palette-system/az-m5ortho/docs/azm5ortho/wifi_setting/README.md

# Wifi設定画面

<br><br>

## 設定画面の開き方
<table>
  <tr>
    <td></td>
    <td valign="top">
      キーボードを設定モードで再起動します。<br>
      設定モードでの再起動の方法はこちら → <a href="https://github.com/palette-system/az-m5ortho/tree/main/docs/azm5ortho/moniter_setting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" target="_blank">https://github.com/palette-system/az-m5ortho/tree/main/docs/azm5ortho/moniter_setting/</a>
    </td>
  </tr>
  <tr>
    <td></td>
    <td valign="top">
      この状態でPCやスマートフォンからWiFiのアクセスポイントを検索すると「<b>AZ-Keyboard-****</b>」があるので接続します。
    </td>
  </tr>
  <tr>
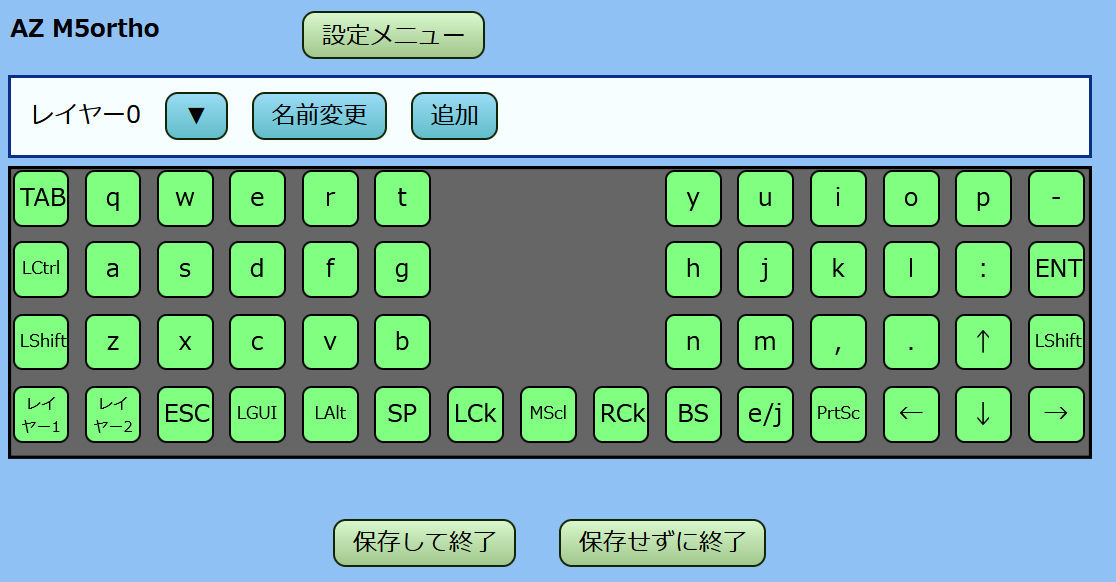
[picture p62: images/azm5ortho/setting_2.jpg]
    <td></td>
    <td valign="top">
      WiFiに接続できるとブラウザが立ち上がり、自動的に設定画面が開きます。
    </td>
  </tr>
</table>

<br><br>

※ 設定画面の操作方法については AZ-Macro の設定マニュアルをご覧下さい。<br>
<a href="https://github.com/palette-system/az-macro/blob/master/docs/az-macro-setting-manual.pdf" target="_blank">AZ-Macro 設定マニュアル</a><br>
<br>
※ アップデートされている箇所がいくつかありますのでこちらのページで少しずつ紹介していきたいと思います。
