palette-system/az-m5ortho/docs/azm5ortho/moniter_setting/README.md

# 液晶画面設定メニュー

<br><br>

## 設定画面の開き方
<table>
  <tr>
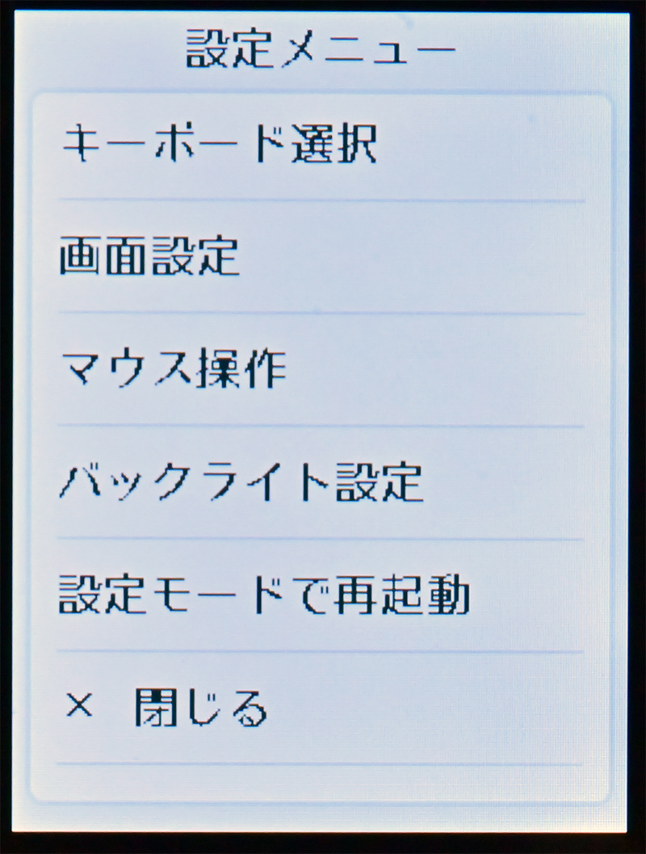
[picture p63: images/azm5ortho/mon_4.jpg]
    <td><br></td>
    <td valign="top">
      待ち受け画面上で、長押しタップ(指を移動させない)すると設定メニューが開かれます。<br><br>
      ※ 待ち受け画像はWiFiアクセスした設定画面から好きな画像に変更できます。
    </td>
  </tr>
</table>

<br><br>

## 各画面の説明
<table>
  <tr>
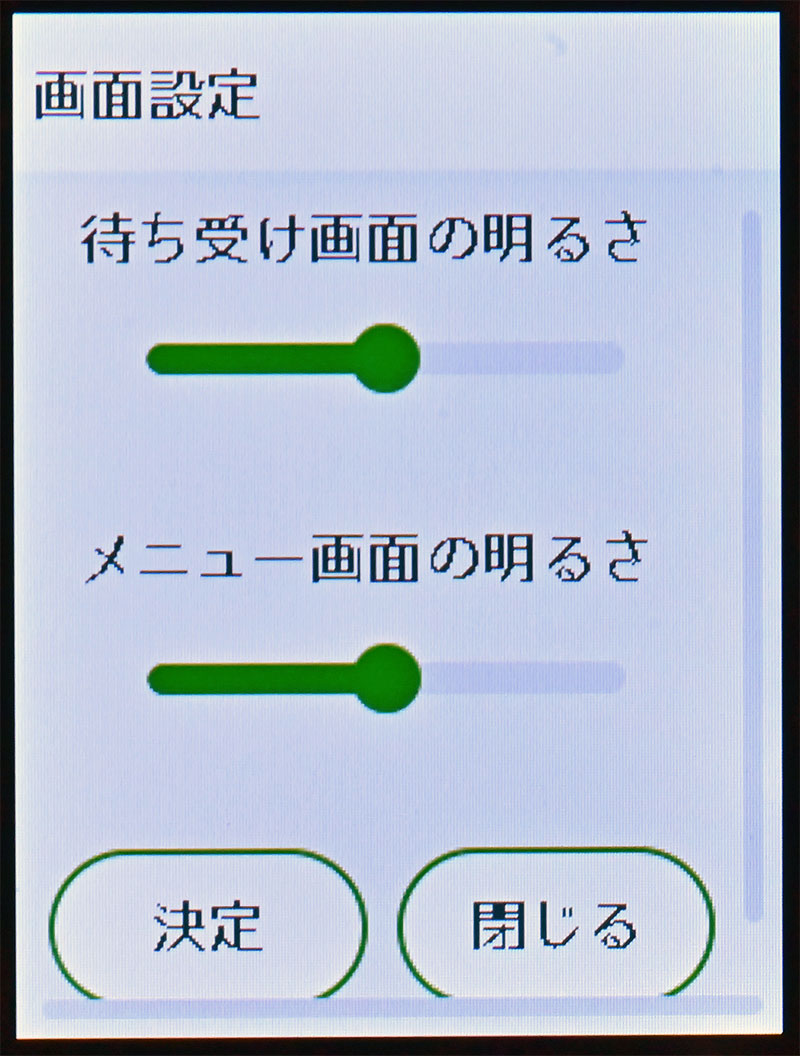
[picture p64: images/azm5ortho/mon_5.jpg]
    <td></td>
    <td valign="top">
      <b>画面設定</b><br><br>
      液晶画面の明るさを設定できます。<br>
      一番左に設定するとバックライトOFFになります。画面は暗い方が電池の持ちが良いです。
    </td>
  </tr>
  <tr>
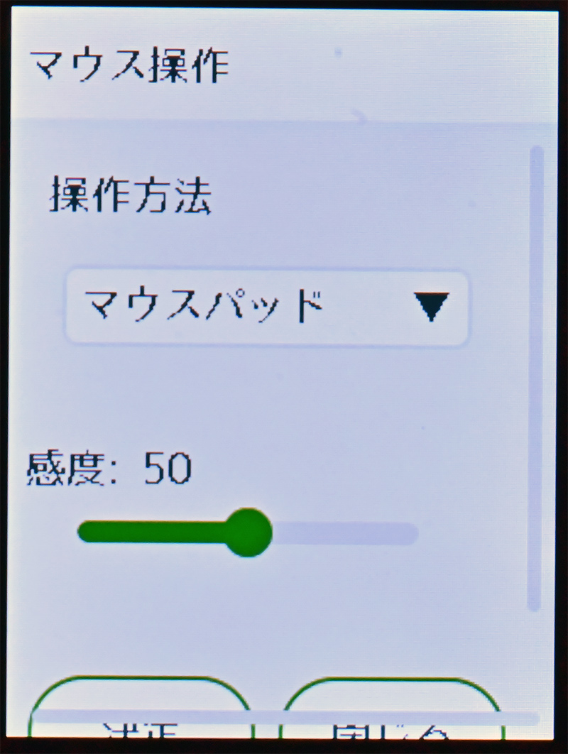
[picture p65: images/azm5ortho/mon_6.jpg]
    <td></td>
    <td valign="top">
      <b>マウス設定</b><br><br>
      待ち受け画面の時の画面タッチの動作を設定できます。<br>
      操作方法は<br>
      <br>
      <b>なし</b>　タッチ動作無し<br>
      <b>マウスパッド</b>　通常のマウスパッド動作<br>
      <b>ジョイスティック</b>　タッチした所から上下左右に動かすとその方向へ動き続ける<br>
      <br>
      から選べます。<br>
      感度は数値が高いほど早く動きます。
    </td>
  </tr>
  <tr>
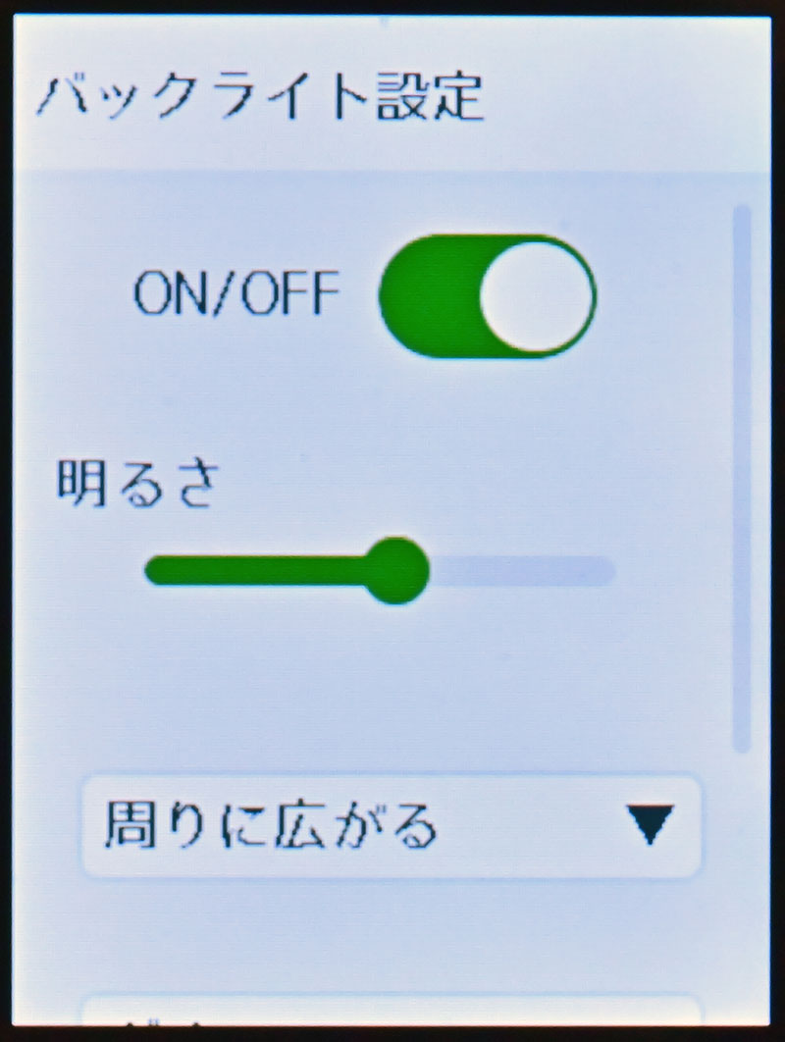
[picture p66: images/azm5ortho/mon_7.jpg]
    <td></td>
    <td valign="top">
      <b>バックライト設定</b><br><br>
      カラーＬＥＤ の ＯＮ／ＯＦＦ や、光らせ方、色などを設定できます。<br><br>
      光り方：<br>
      <b>常に点灯</b>　常に光らせます<br>
      <b>押したら点灯</b>　ボタンを押した時だけ光ります<br>
      <b>周りに広がる</b>　ボタンを押した所から周りに広がります<br>
      <b>グラデーション</b>　常に全LEDがグラデーションします<br>
      <br>
      色：<br>
      ホワイト ／ レッド ／ グリーン ／ ブルー ／ スカイブルー ／ イエロー
    </td>
  </tr>
  <tr>
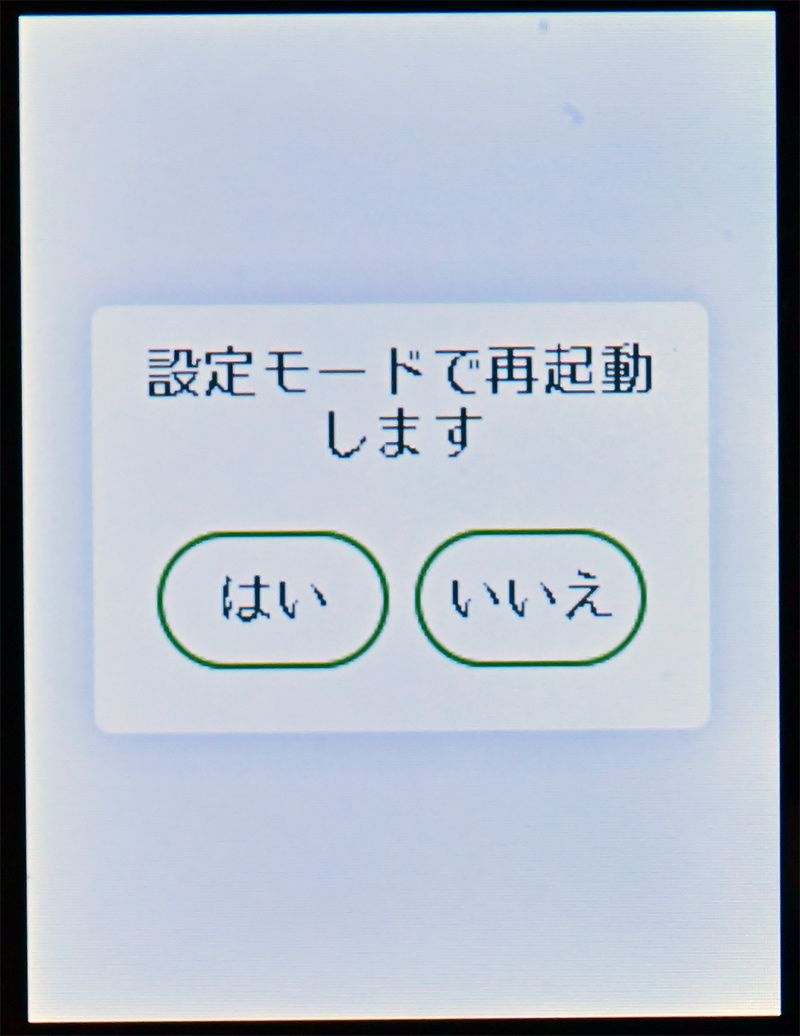
[picture p67: images/azm5ortho/mon_8.jpg]
    <td><br></td>
    <td valign="top">
      <b>設定モードで再起動</b><br><br>
      キーボードを設定モードでキーボードを再起動します。<br>
      設定モードで起動するとWiFiからキーボードにアクセスできるようになり、より細かい設定が可能になります。<br>
      <br>
      ※ 設定モード中はキーボードとして動作しません。
    </td>
  </tr>
</table>
