palette-system/az-m5ortho/firmware/aztool/img/mcp23017.png

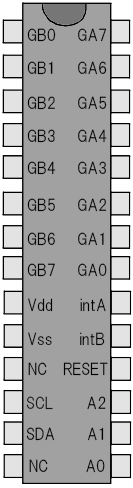
firmware/aztool/img/mcp23017.png
