palette-system/az-m5ortho/images/azm5ortho/comp_1.jpg

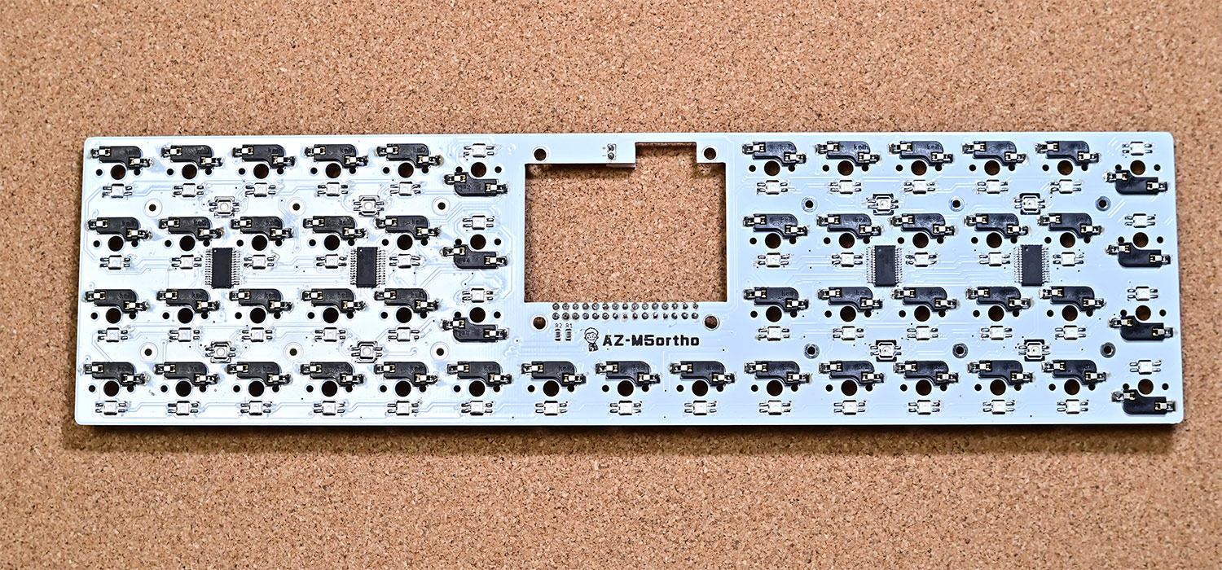
images/azm5ortho/comp_1.jpg
