palette-system/az-m5ortho/images/azm5ortho/init_1.jpg

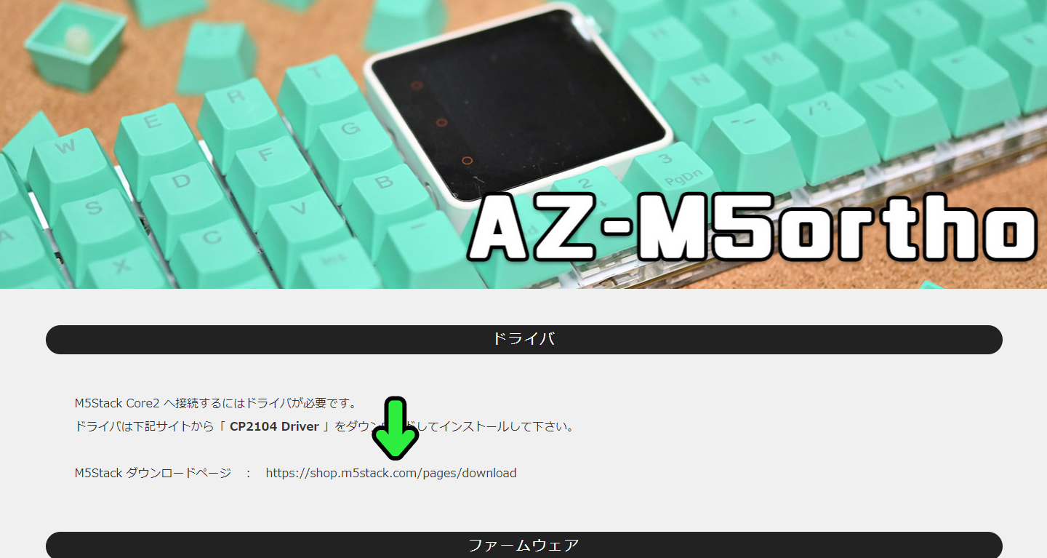
images/azm5ortho/init_1.jpg
