palette-system/az-m5ortho/images/azm5ortho/mon_2.jpg

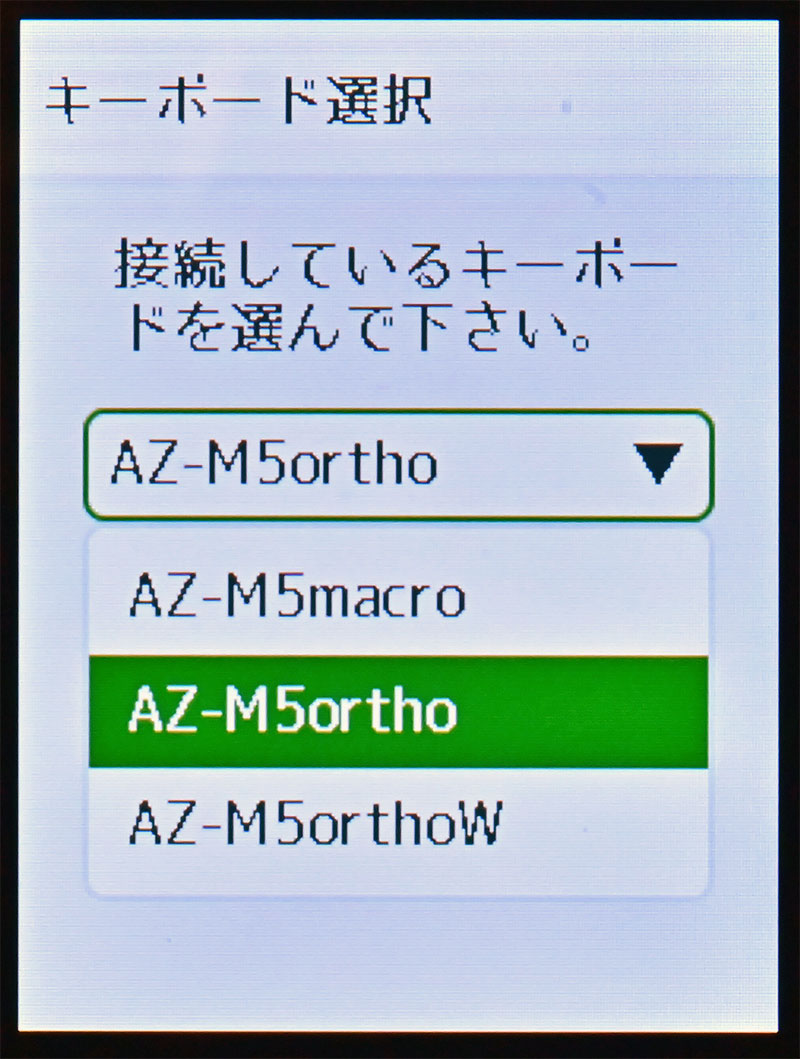
images/azm5ortho/mon_2.jpg
