palette-system/az-m5ortho/images/emugotch/booth_3.jpg

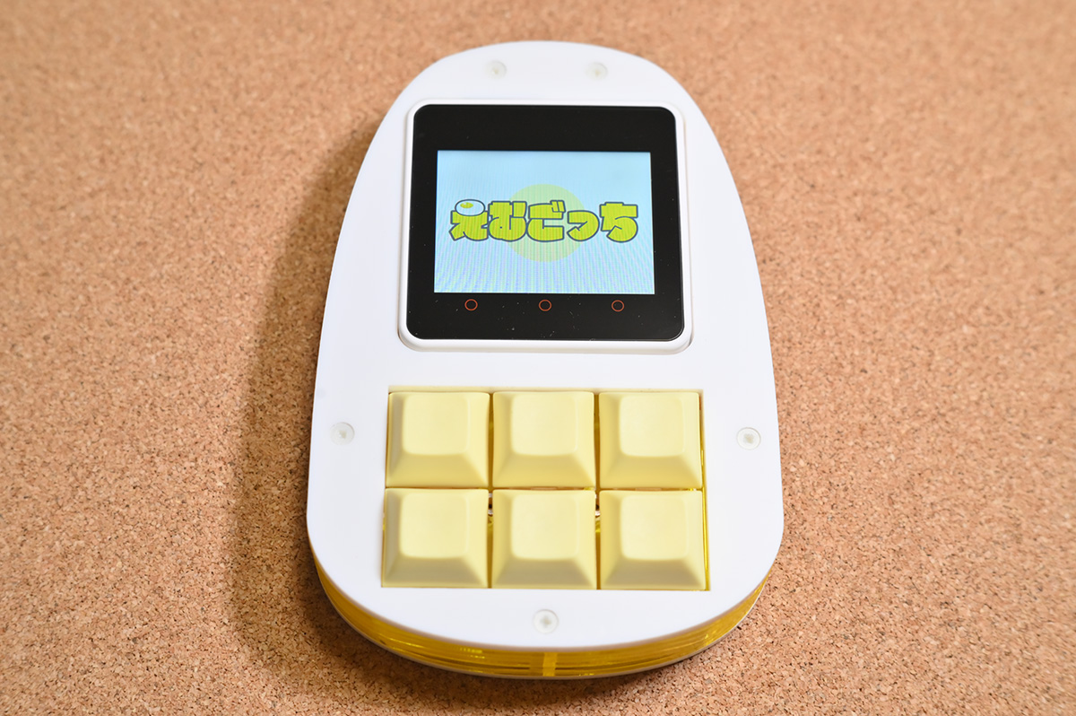
images/emugotch/booth_3.jpg
