palette-system/az-m5ortho/images/emugotch/booth_in.jpg

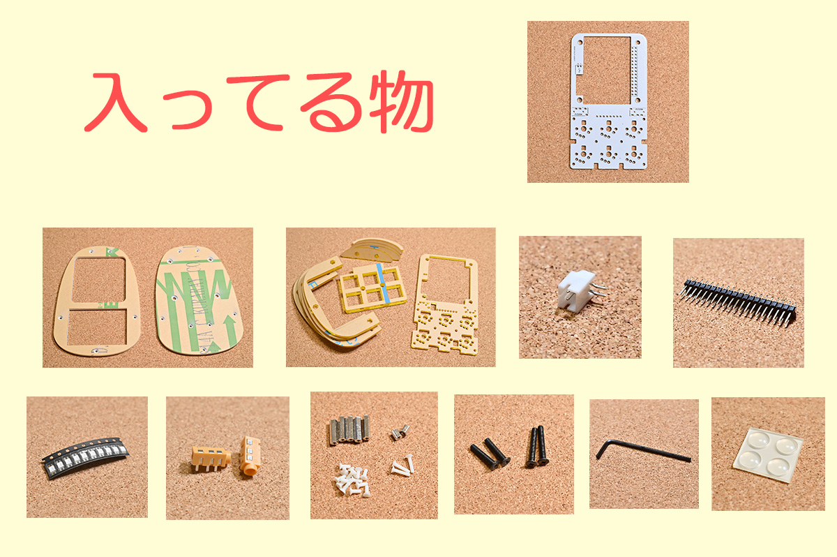
images/emugotch/booth_in.jpg
