palette-system/az-m5ortho/images/setting/create_wav_05.png

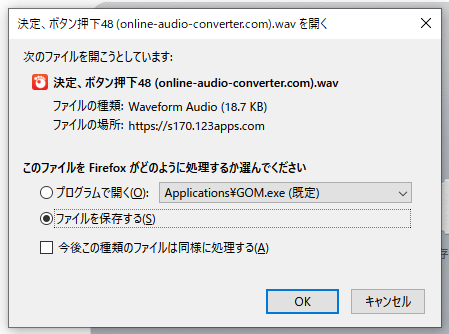
images/setting/create_wav_05.png
